H4Lab/H4_EtherCAT_6-Port_Module/Diagram.png

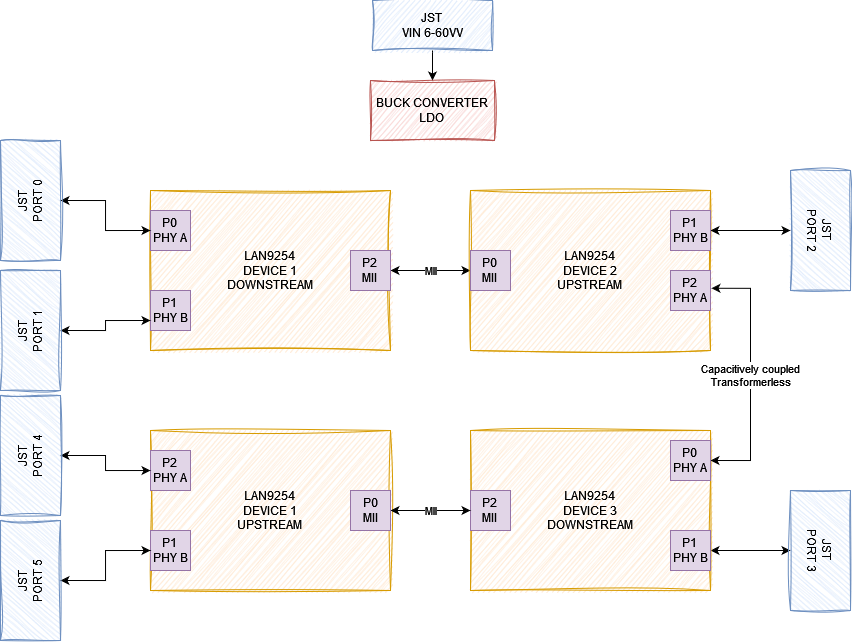
Diagram.png
