H4Lab/H4_EtherCAT_6-Port_Module/Documentation/Images/1.jpg

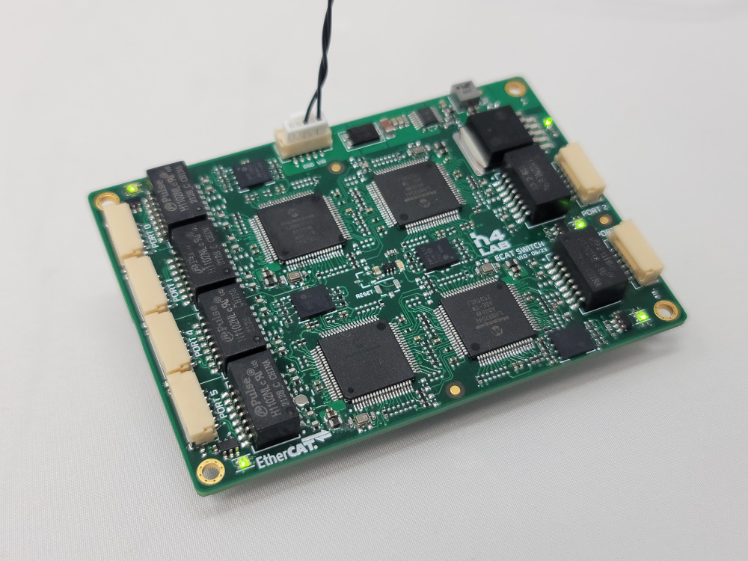
Documentation/Images/1.jpg
