H4Lab/H4_EtherCAT_6-Port_Module/Documentation/Images/2.jpg

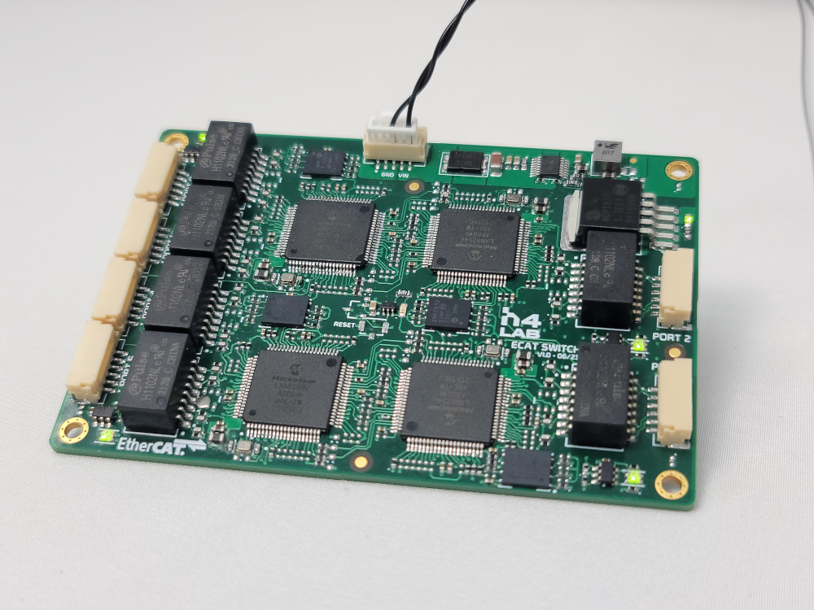
Documentation/Images/2.jpg
