H4Lab/H4_EtherCAT_6-Port_Module/Documentation/Images/4.jpeg

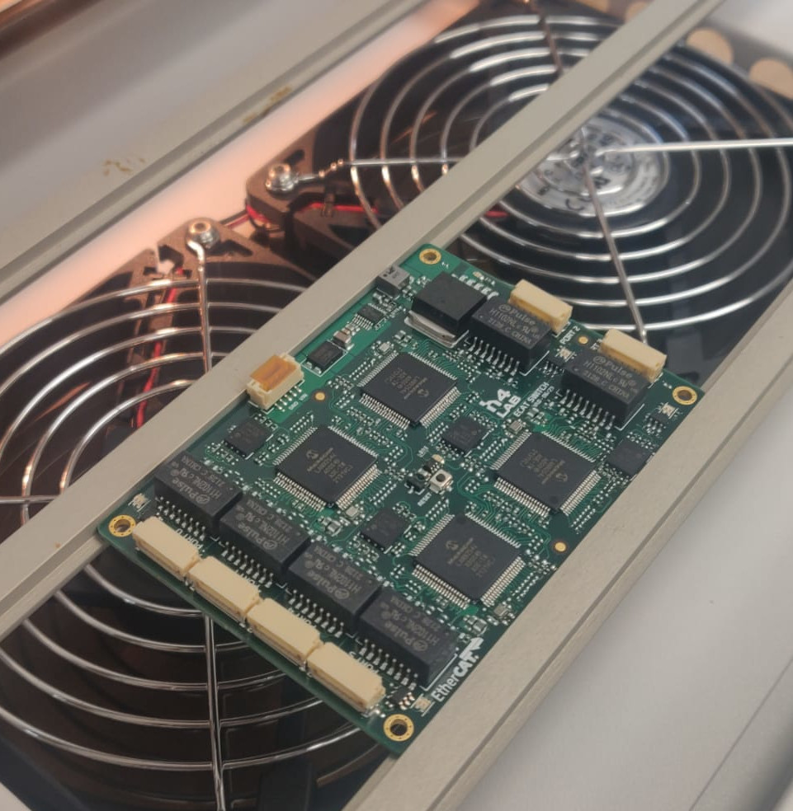
Documentation/Images/4.jpeg
